Avishkar1312/6-DOF-Robotic-Arm/Circuit_diagrams/Servo_motor_connections.png

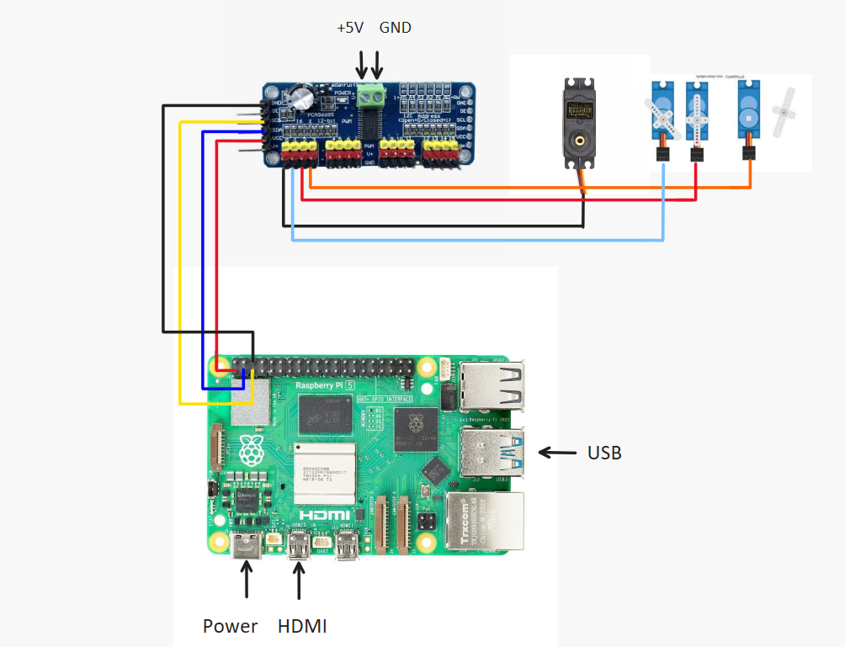
Circuit_diagrams/Servo_motor_connections.png
