Avishkar1312/6-DOF-Robotic-Arm/Circuit_diagrams/Stepper_motor_connections.png

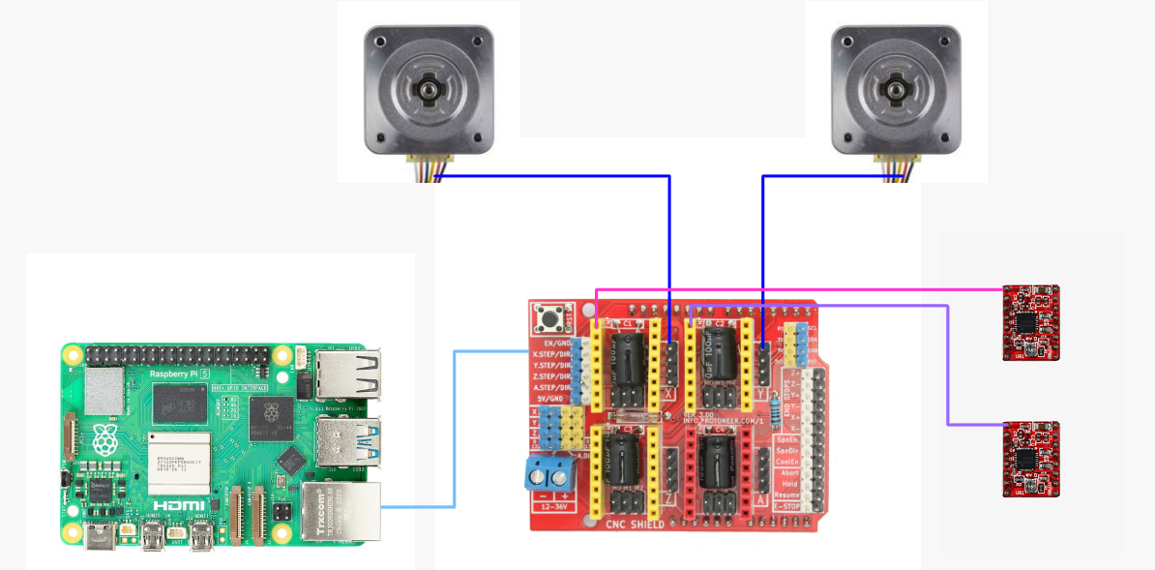
Circuit_diagrams/Stepper_motor_connections.png
