Avishkar1312/6-DOF-Robotic-Arm/img/servos.jpg

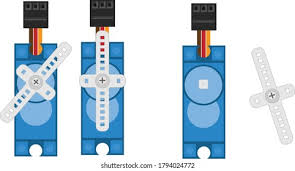
img/servos.jpg
