Avishkar1312/6-DOF-Robotic-Arm/Cad_files/wrist _rotation_lid.SLDPRT

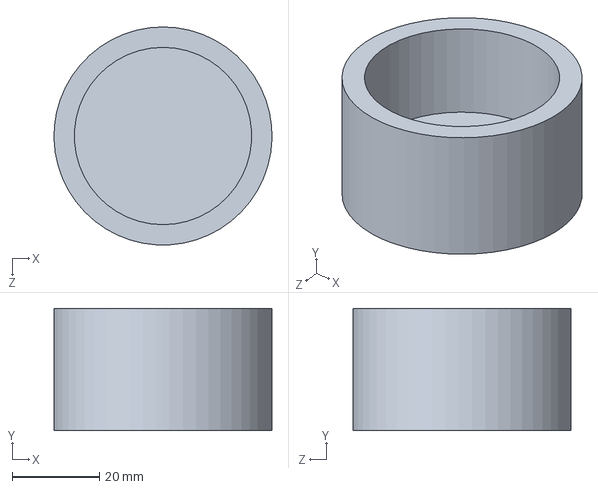
[picture p37: CAD file, 2025-05-11]
Cad_files/wrist _rotation_lid.SLDPRT
50.0 x 28.0 x 50.0 mm
