Avishkar1312/6-DOF-Robotic-Arm/Cad_files/[4145] TowerPro SG90 Mini Servo-SunRobotics_in-Pt4.SLDPRT

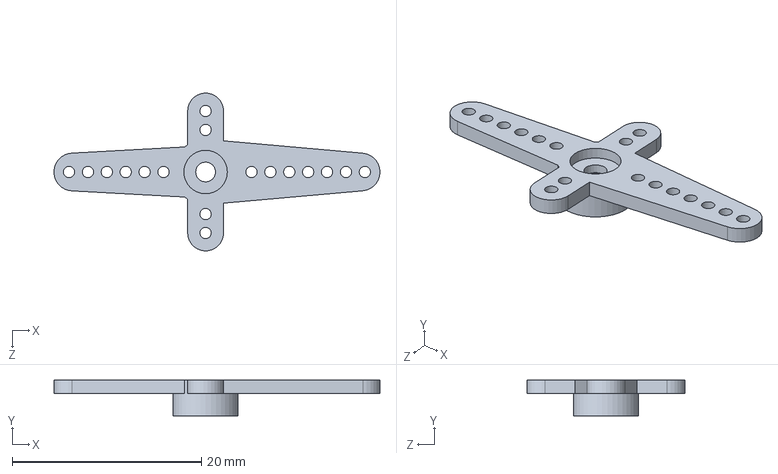
[picture p38: CAD file, 2025-05-11]
Cad_files/[4145] TowerPro SG90 Mini Servo-SunRobotics_in-Pt4.SLDPRT
34.5 x 3.80 x 16.7 mm
