Avishkar1312/6-DOF-Robotic-Arm/Cad_files/mg995.stp

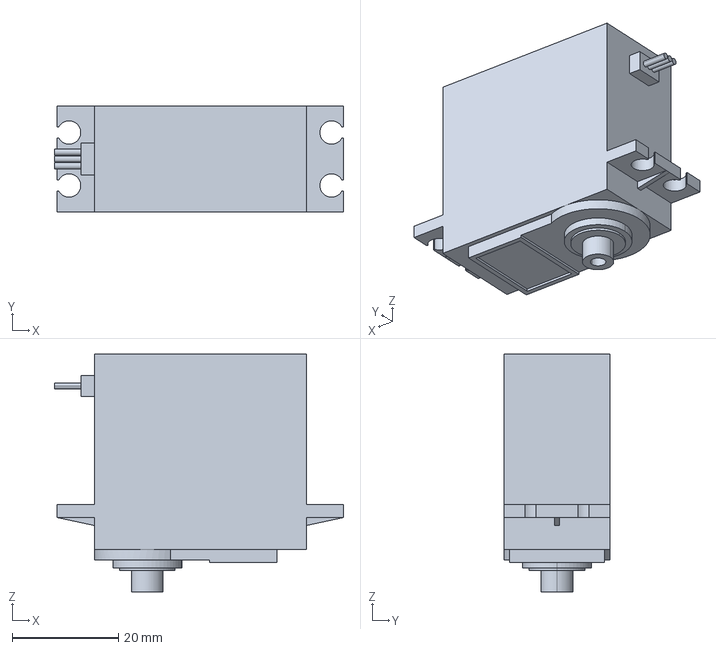
[picture p40: CAD file, 2025-05-11]
Cad_files/mg995.stp
54.5 x 20.0 x 44.8 mm
