Avishkar1312/6-DOF-Robotic-Arm/Cad_files/gripper.SLDPRT

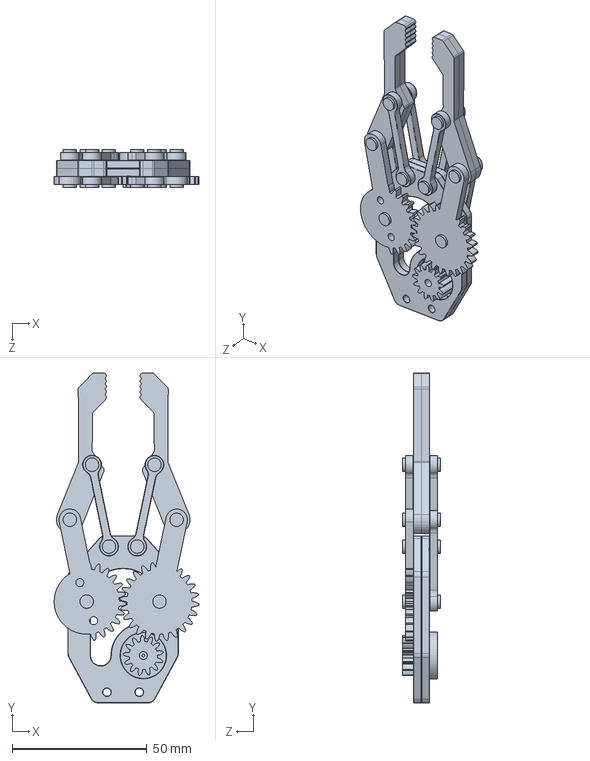
[picture p41: CAD file, 2025-05-11]
Cad_files/gripper.SLDPRT
53.7 x 122.4 x 14.0 mm
