Avishkar1312/6-DOF-Robotic-Arm/Cad_files/plug.SLDPRT

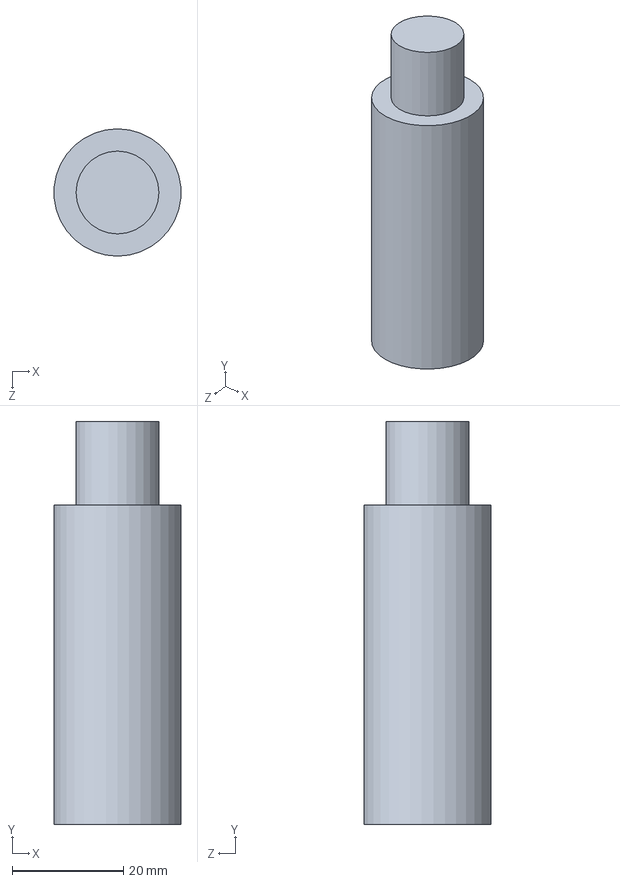
[picture p42: CAD file, 2025-05-11]
Cad_files/plug.SLDPRT
22.8 x 72.5 x 22.9 mm
