Avishkar1312/6-DOF-Robotic-Arm/Cad_files/basetop.SLDPRT

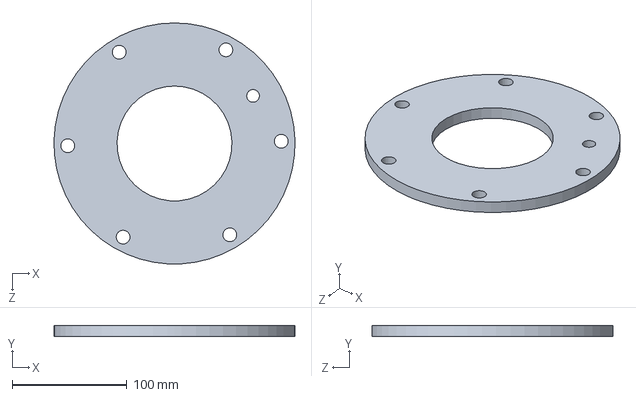
[picture p43: CAD file, 2025-05-11]
Cad_files/basetop.SLDPRT
209.9 x 10.0 x 210.0 mm
