Avishkar1312/6-DOF-Robotic-Arm/Cad_files/arm.SLDPRT

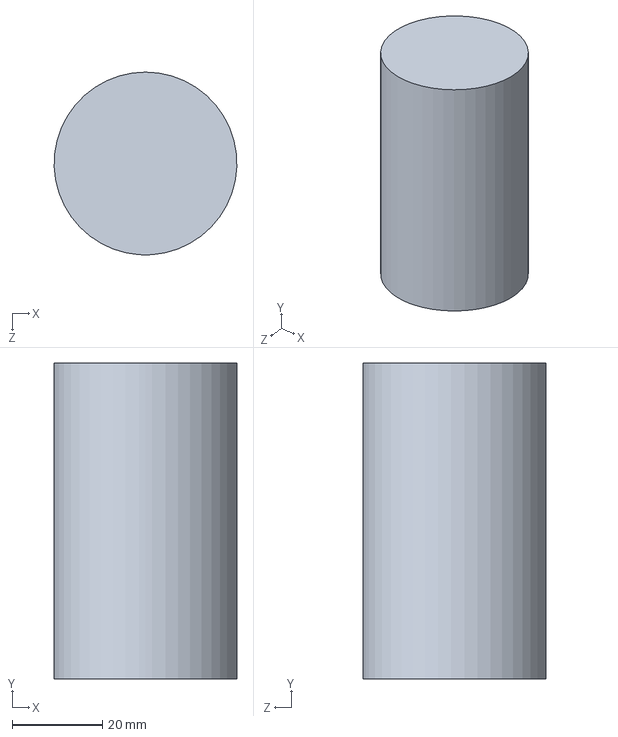
[picture p44: CAD file, 2025-05-11]
Cad_files/arm.SLDPRT
40.5 x 70.0 x 40.5 mm
