Avishkar1312/6-DOF-Robotic-Arm/Cad_files/NEMA_17.SLDPRT

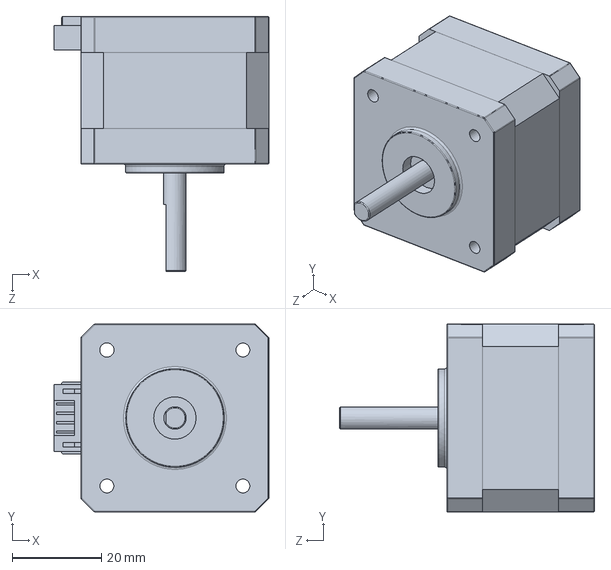
[picture p45: CAD file, 2025-05-11]
Cad_files/NEMA_17.SLDPRT
48.0 x 42.0 x 57.0 mm
