Avishkar1312/6-DOF-Robotic-Arm/Cad_files/wristholder.SLDPRT

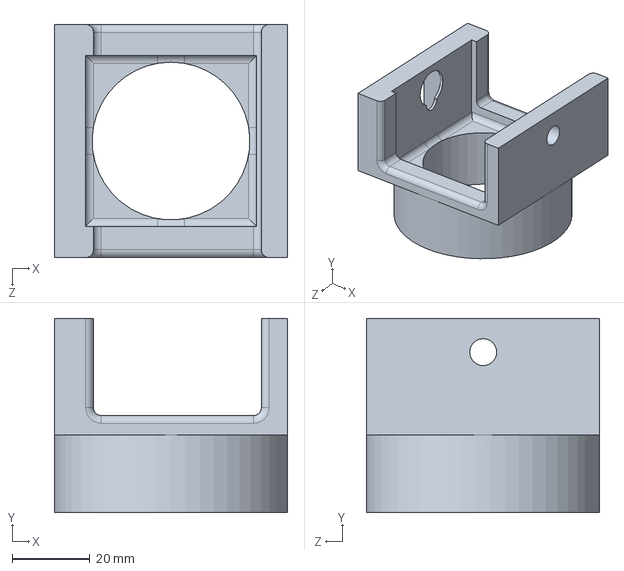
[picture p46: CAD file, 2025-05-11]
Cad_files/wristholder.SLDPRT
60.0 x 50.0 x 60.0 mm
