Avishkar1312/6-DOF-Robotic-Arm/Cad_files/pinpin.SLDPRT

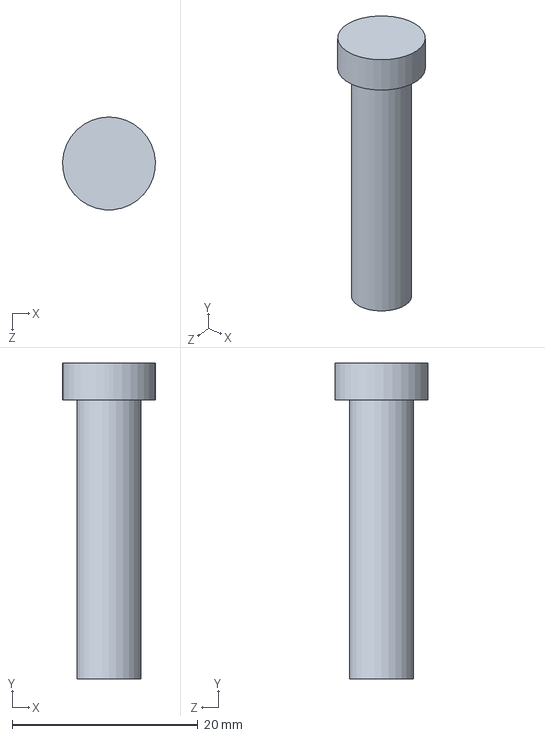
[picture p47: CAD file, 2025-05-11]
Cad_files/pinpin.SLDPRT
9.99 x 34.0 x 10.0 mm
