Avishkar1312/6-DOF-Robotic-Arm/Cad_files/large_gear.SLDPRT

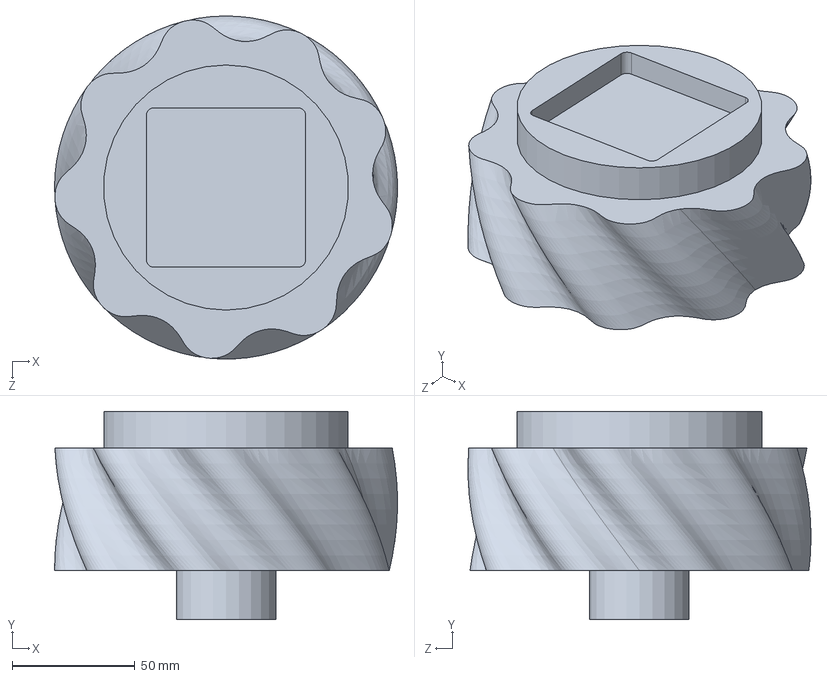
[picture p48: CAD file, 2025-05-11]
Cad_files/large_gear.SLDPRT
140.0 x 85.0 x 140.0 mm
