Avishkar1312/6-DOF-Robotic-Arm/Cad_files/Servo SG90.SLDPRT

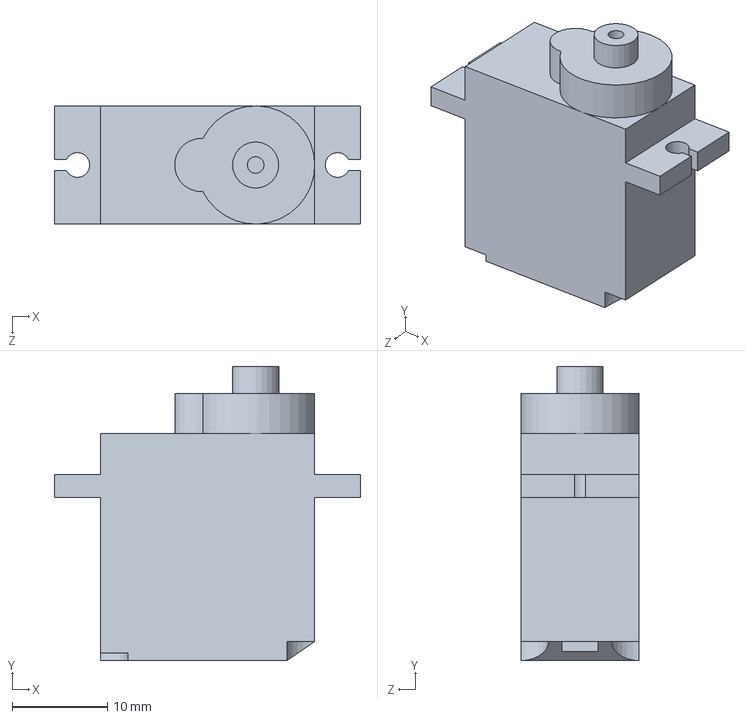
[picture p49: CAD file, 2025-05-11]
Cad_files/Servo SG90.SLDPRT
32.1 x 30.9 x 12.4 mm
