Avishkar1312/6-DOF-Robotic-Arm/Cad_files/Part7.SLDPRT

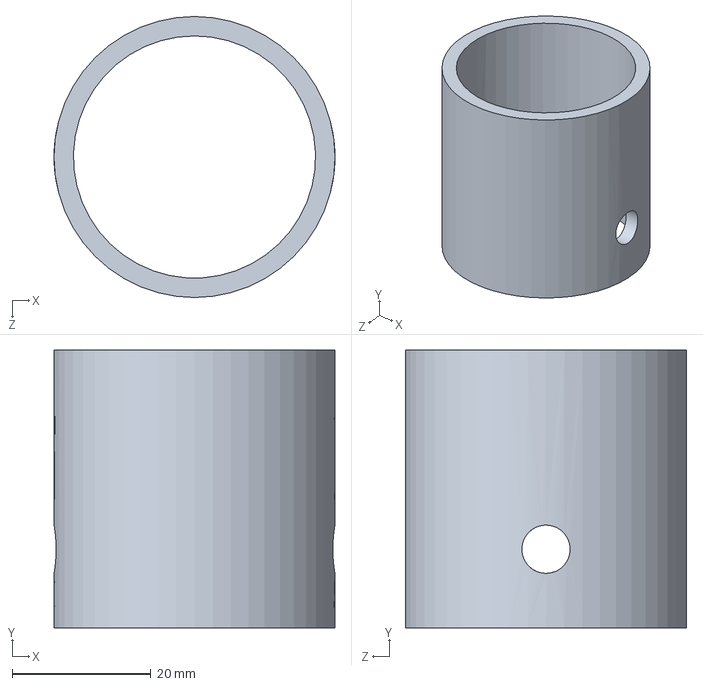
[picture p50: CAD file, 2025-05-11]
Cad_files/Part7.SLDPRT
40.5 x 40.0 x 40.5 mm
