Avishkar1312/6-DOF-Robotic-Arm/Cad_files/instrument ball bearing_68_am.sldprt

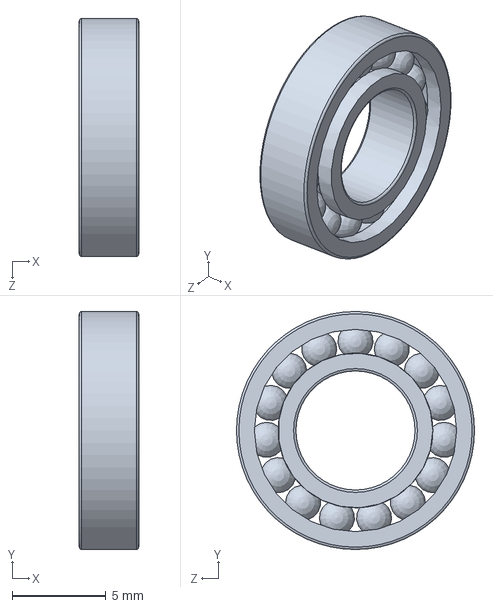
[picture p51: CAD file, 2025-05-11]
Cad_files/instrument ball bearing_68_am.sldprt
3.17 x 12.7 x 12.7 mm
