Avishkar1312/6-DOF-Robotic-Arm/Cad_files/blue_servo_mod_teeth.SLDPRT

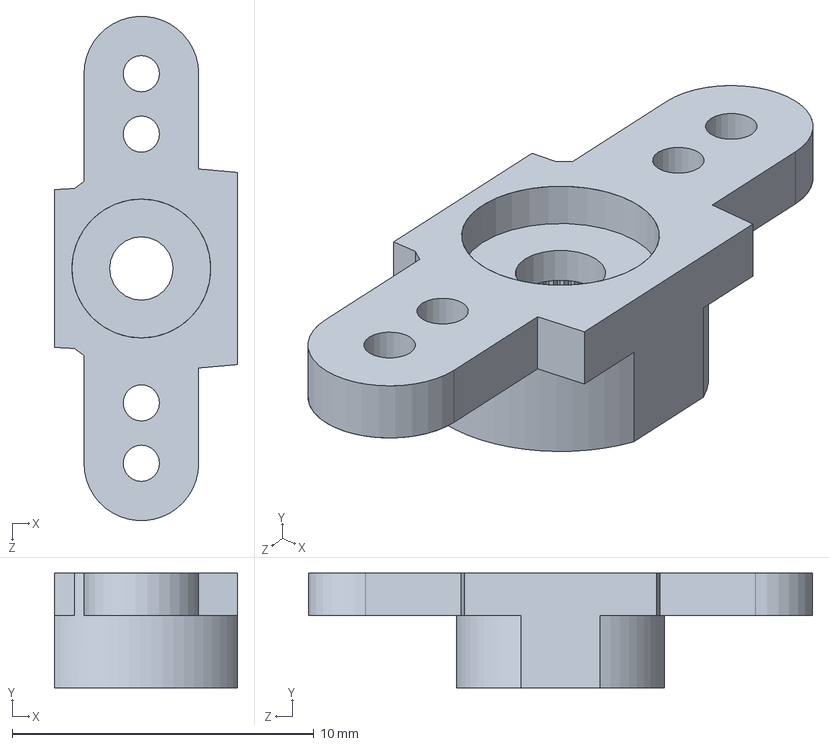
[picture p52: CAD file, 2025-05-11]
Cad_files/blue_servo_mod_teeth.SLDPRT
6.07 x 3.80 x 16.7 mm
