Avishkar1312/6-DOF-Robotic-Arm/Cad_files/Part9.SLDPRT

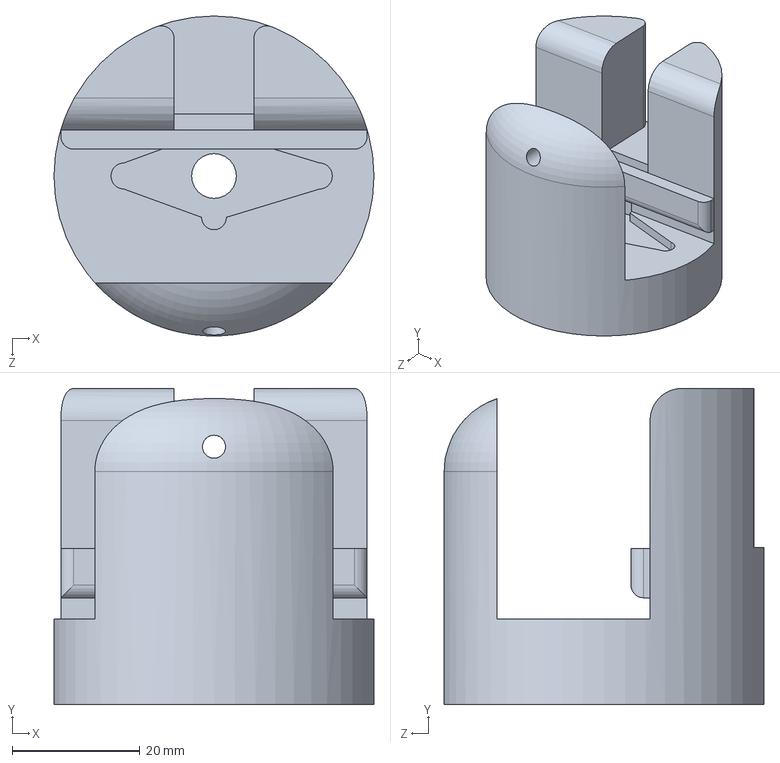
[picture p53: CAD file, 2025-05-11]
Cad_files/Part9.SLDPRT
50.0 x 49.4 x 50.0 mm
