Avishkar1312/6-DOF-Robotic-Arm/Cad_files/small_gear.SLDPRT

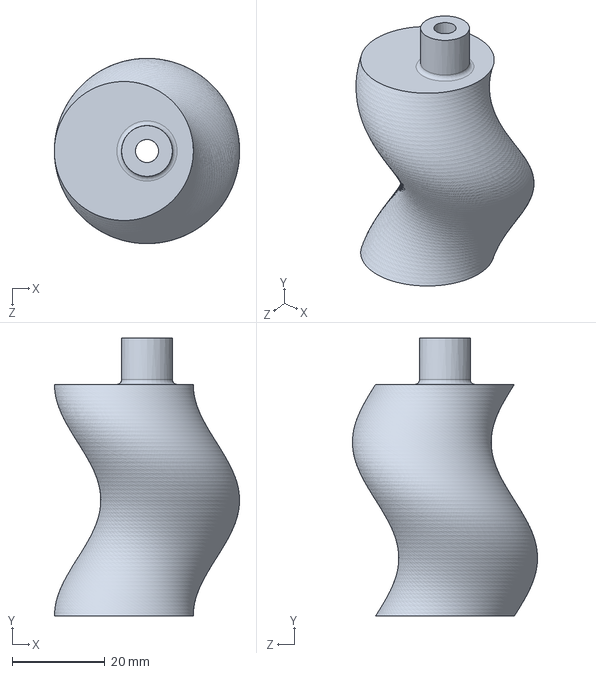
[picture p54: CAD file, 2025-05-11]
Cad_files/small_gear.SLDPRT
40.0 x 60.0 x 40.0 mm
