Avishkar1312/6-DOF-Robotic-Arm/Cad_files/final_shoulder.SLDPRT

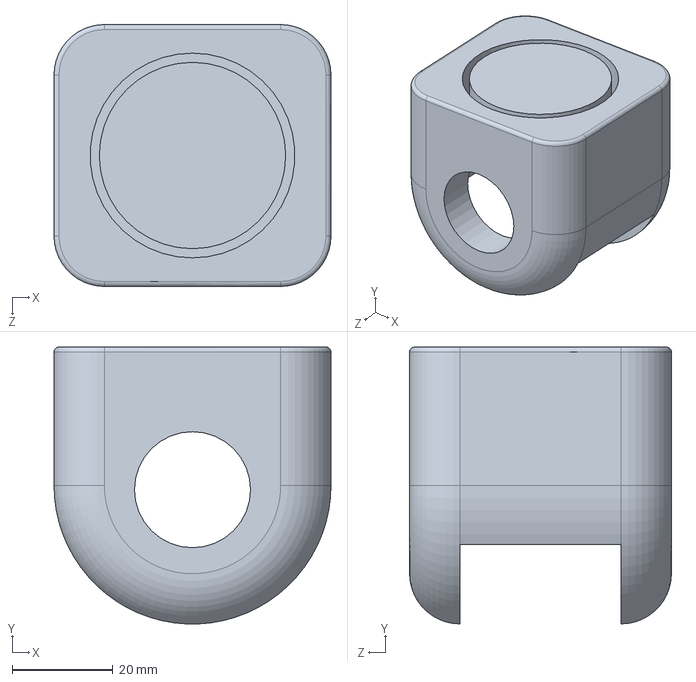
[picture p55: CAD file, 2025-05-11]
Cad_files/final_shoulder.SLDPRT
55.0 x 55.0 x 52.0 mm
